FabianWildgrube/NodeMCU-Wifi-Power-Socket/images/IMG_0125.JPG

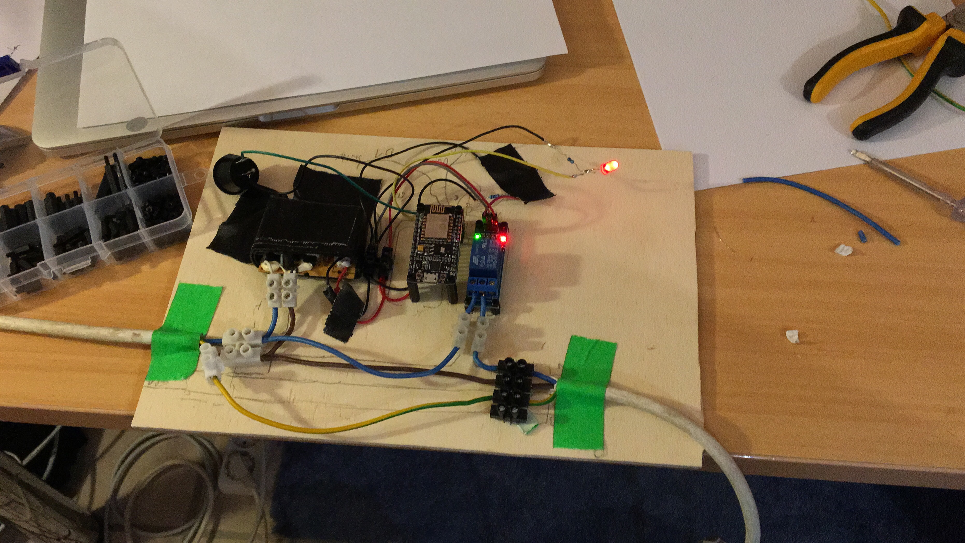
images/IMG_0125.JPG
