FabianWildgrube/NodeMCU-Wifi-Power-Socket/images/IMG_0147.JPG

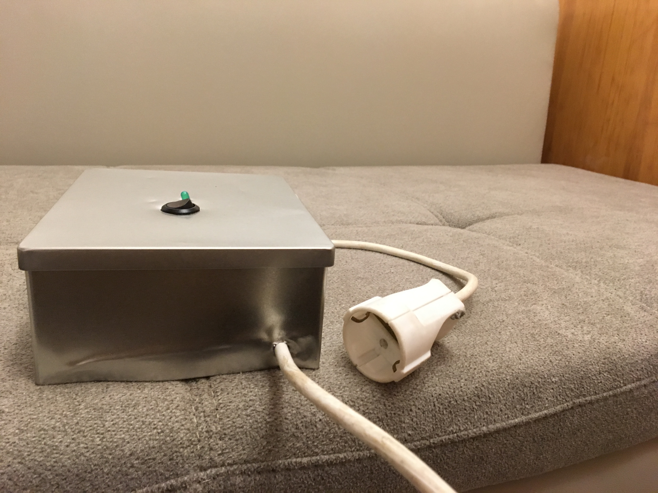
images/IMG_0147.JPG
